maboytim/TRS-80_Display_Adapter/fpga/vid80-1/src/gowin_dpb/gowin_dpb_tmp.v

//Copyright (C)2014-2024 Gowin Semiconductor Corporation.
//All rights reserved.
//File Title: Template file for instantiation
//Tool Version: V1.9.9.03 Education (64-bit)
//Part Number: GW1NR-LV9QN88PC6/I5
//Device: GW1NR-9
//Device Version: C
//Created Time: Fri Dec 13 01:37:41 2024

//Change the instance name and port connections to the signal names
//--------Copy here to design--------

    Gowin_DPB your_instance_name(
        .douta(douta), //output [5:0] douta
        .doutb(doutb), //output [5:0] doutb
        .clka(clka), //input clka
        .ocea(ocea), //input ocea
        .cea(cea), //input cea
        .reseta(reseta), //input reseta
        .wrea(wrea), //input wrea
        .clkb(clkb), //input clkb
        .oceb(oceb), //input oceb
        .ceb(ceb), //input ceb
        .resetb(resetb), //input resetb
        .wreb(wreb), //input wreb
        .ada(ada), //input [13:0] ada
        .dina(dina), //input [5:0] dina
        .adb(adb), //input [13:0] adb
        .dinb(dinb) //input [5:0] dinb
    );

//--------Copy end-------------------
