maboytim/TRS-80_Display_Adapter/fpga/vid80-1/src/gowin_osc/gowin_osc_tmp.v

//Copyright (C)2014-2022 Gowin Semiconductor Corporation.
//All rights reserved.
//File Title: Template file for instantiation
//GOWIN Version: V1.9.8.05
//Part Number: GW1NR-LV9QN88PC6/I5
//Device: GW1NR-9C
//Created Time: Wed Jun 22 23:55:49 2022

//Change the instance name and port connections to the signal names
//--------Copy here to design--------

    Gowin_OSC your_instance_name(
        .oscout(oscout_o) //output oscout
    );

//--------Copy end-------------------
